anichno/bluetooth-scanner-bracer/kicad/bluetooth-scanner-bracer.kicad_sch

## KiCad design kicad/bluetooth-scanner-bracer.kicad_sch (2023-03-10)

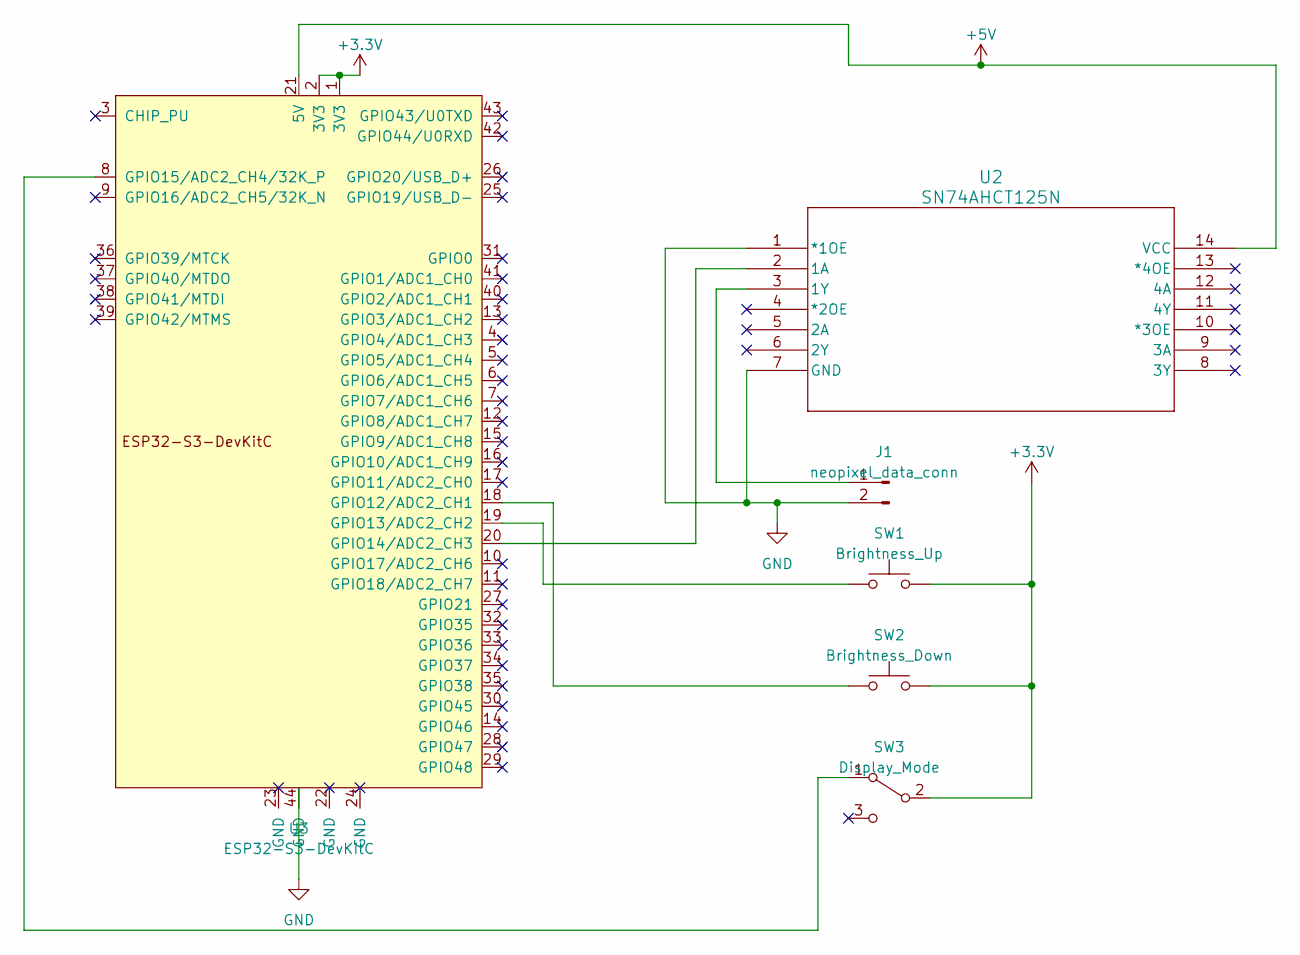
[picture p3: schematic bluetooth-scanner-bracer.kicad_sch]

Parts:
J1: neopixel_data_conn
SW1: Brightness_Up
SW2: Brightness_Down
SW3: Display_Mode
U2: SN74AHCT125N; N14
U3: ESP32-S3-DevKitC

Connections:
+3.3V: SW1.2, SW2.2, SW3.2 (B), U3.1 (3V3), U3.2 (3V3)
+5V: U2.14 (VCC), U3.21 (5V)
GND: J1.2 (GND), U2.1 (*1OE), U2.7 (GND), U3.44 (GND)
unnamed: J1.1 (Data), U2.3 (1Y)
unnamed: SW1.1, U3.19 (GPIO13/ADC2_CH2)
unnamed: SW2.1, U3.18 (GPIO12/ADC2_CH1)
unnamed: SW3.1 (A), U3.8 (GPIO15/ADC2_CH4/32K_P)
unnamed: U2.2 (1A), U3.20 (GPIO14/ADC2_CH3)
